GeiserX/PiSpot-Watch/docs/photos/board-stack-battery-wires-side.jpg

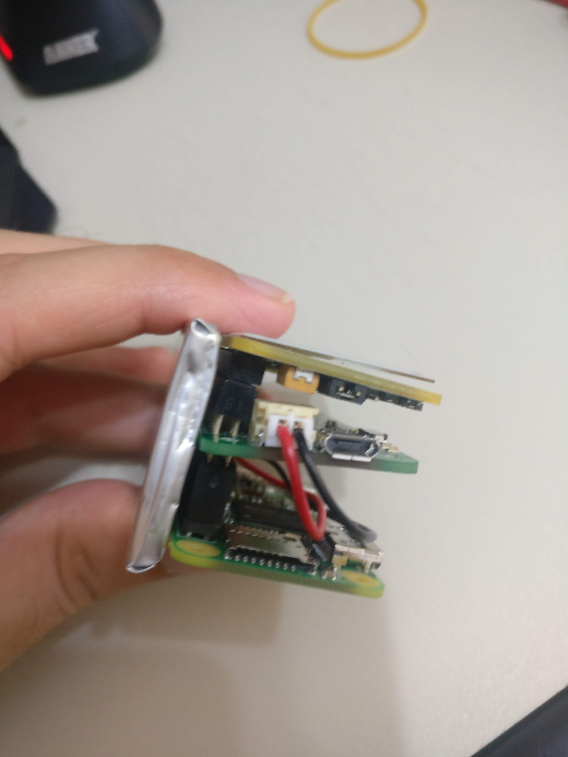
docs/photos/board-stack-battery-wires-side.jpg
