GeiserX/PiSpot-Watch/docs/photos/board-stack-blank-eink-sdcard.jpg

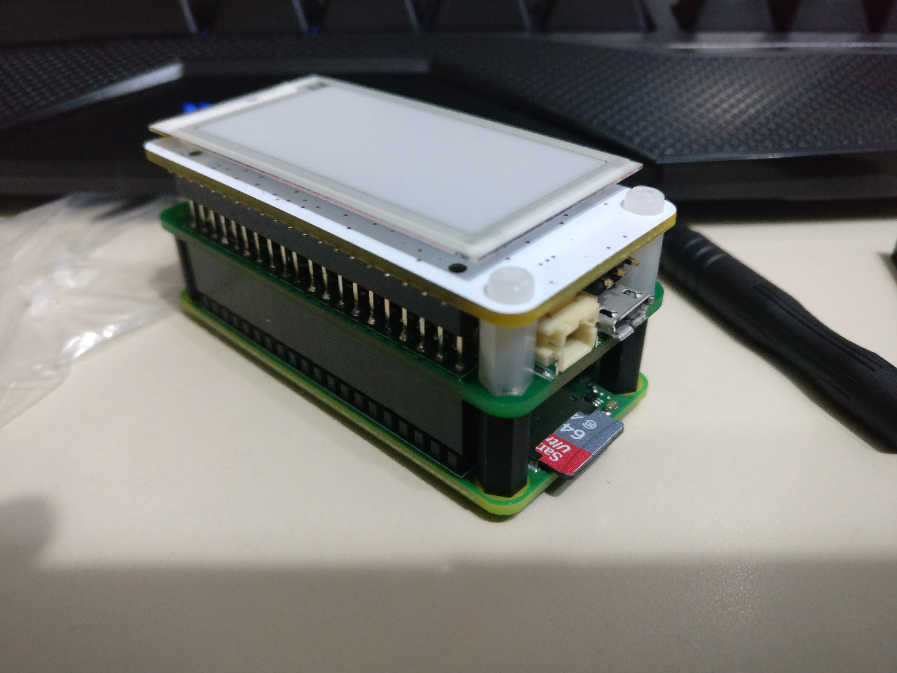
docs/photos/board-stack-blank-eink-sdcard.jpg
