GeiserX/PiSpot-Watch/docs/photos/board-stack-brass-standoffs-front.jpg

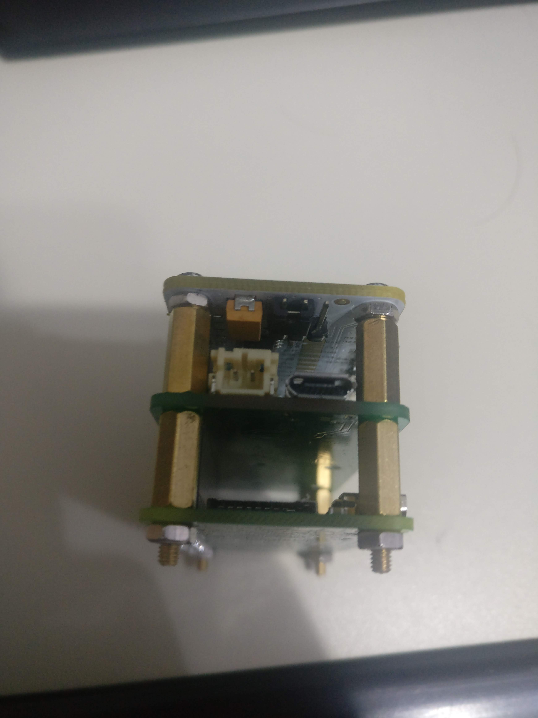
docs/photos/board-stack-brass-standoffs-front.jpg
