GeiserX/PiSpot-Watch/docs/photos/board-stack-brass-standoffs-side.jpg

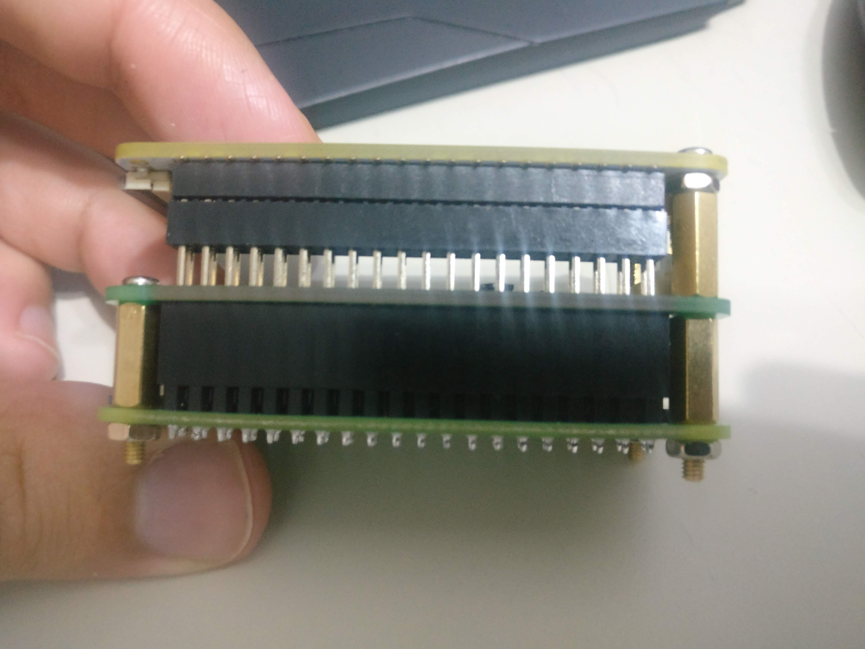
docs/photos/board-stack-brass-standoffs-side.jpg
