GeiserX/PiSpot-Watch/docs/photos/board-stack-in-hand.jpg

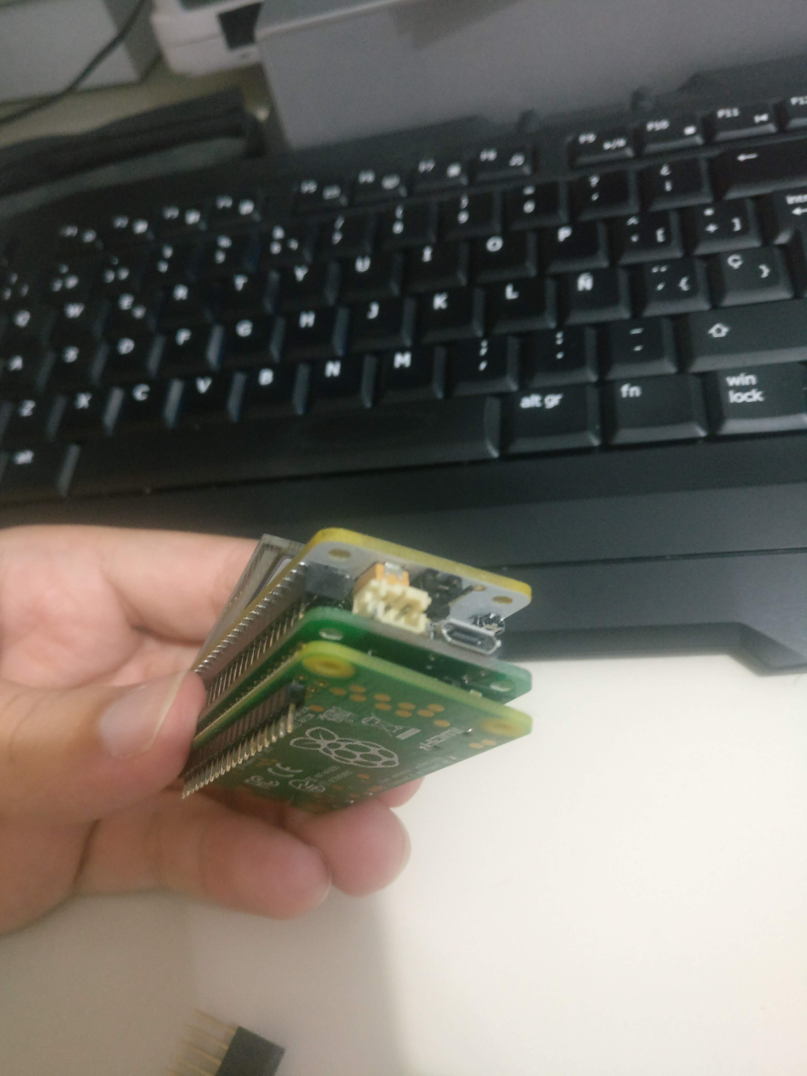
docs/photos/board-stack-in-hand.jpg
