GeiserX/PiSpot-Watch/docs/photos/board-stack-side-profile.jpg

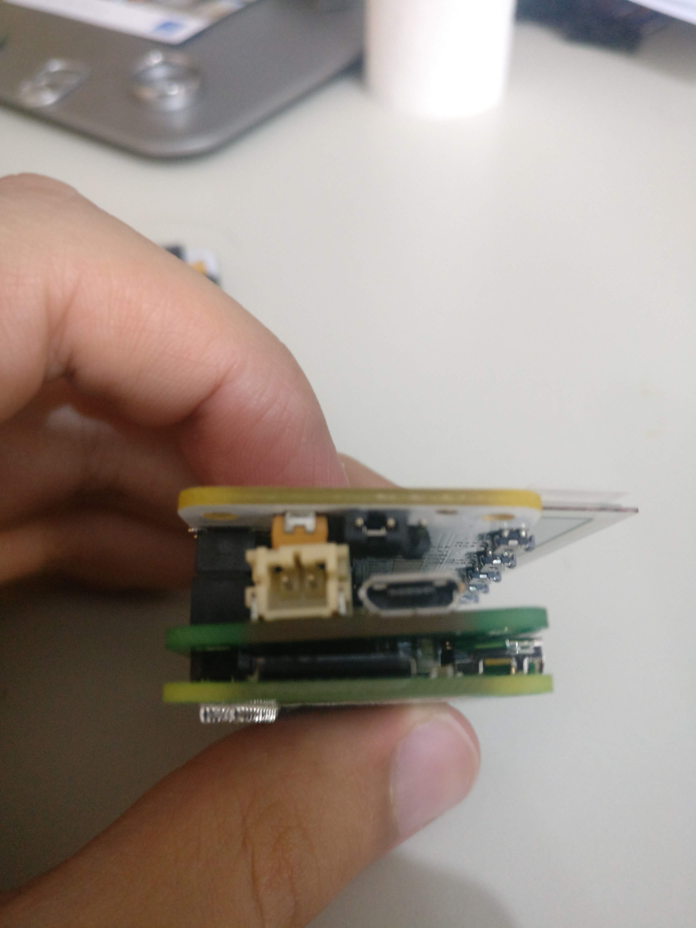
docs/photos/board-stack-side-profile.jpg
