GeiserX/PiSpot-Watch/docs/photos/board-stack-with-battery-side.jpg

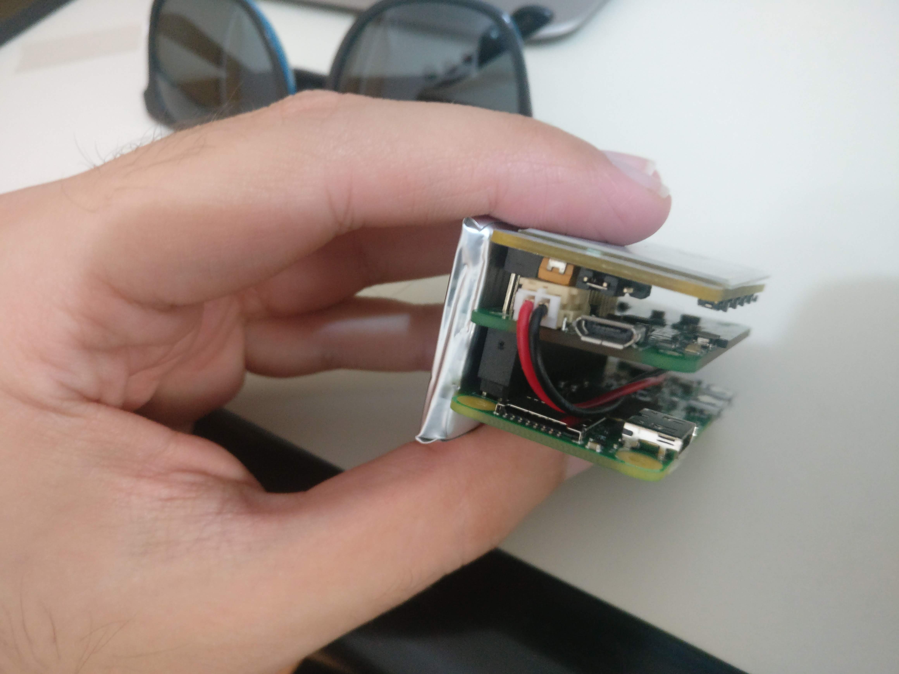
docs/photos/board-stack-with-battery-side.jpg
