GeiserX/PiSpot-Watch/docs/photos/button-panel-side-view.jpg

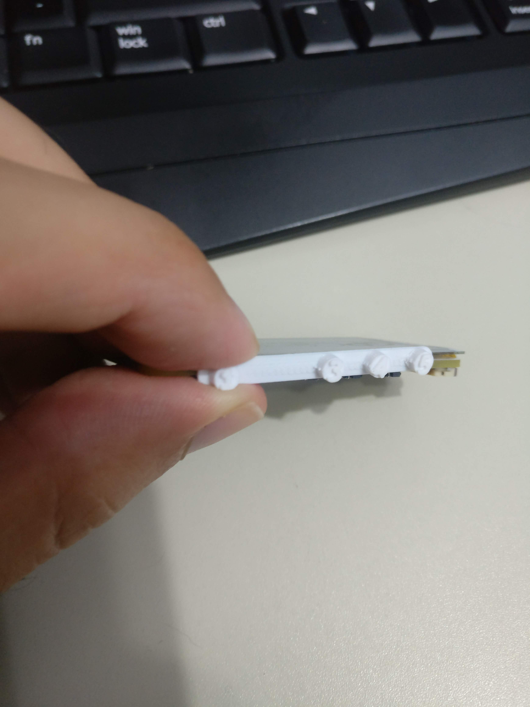
docs/photos/button-panel-side-view.jpg
