GeiserX/PiSpot-Watch/docs/photos/lipo-batteries-1200mah.jpg

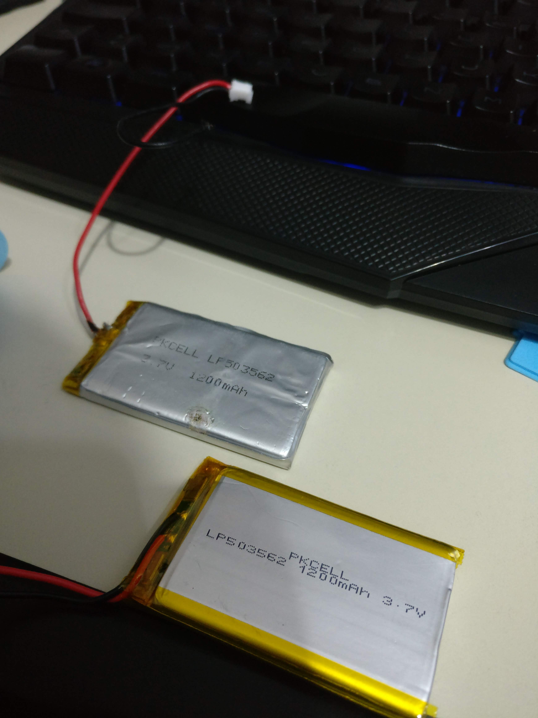
docs/photos/lipo-batteries-1200mah.jpg
