GeiserX/PiSpot-Watch/docs/photos/pi-zero-w-board-back.jpg

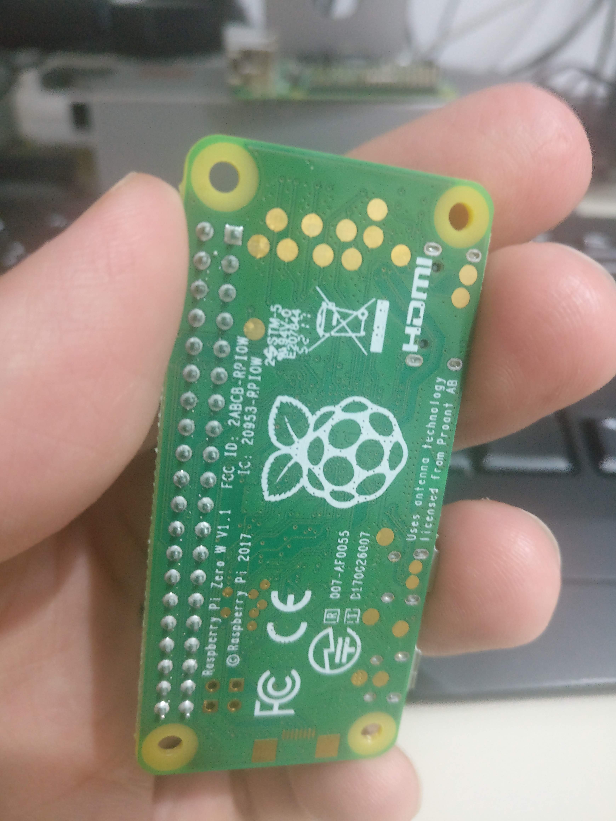
docs/photos/pi-zero-w-board-back.jpg
