GeiserX/PiSpot-Watch/docs/photos/watch-black-case-hdmi-side.jpg

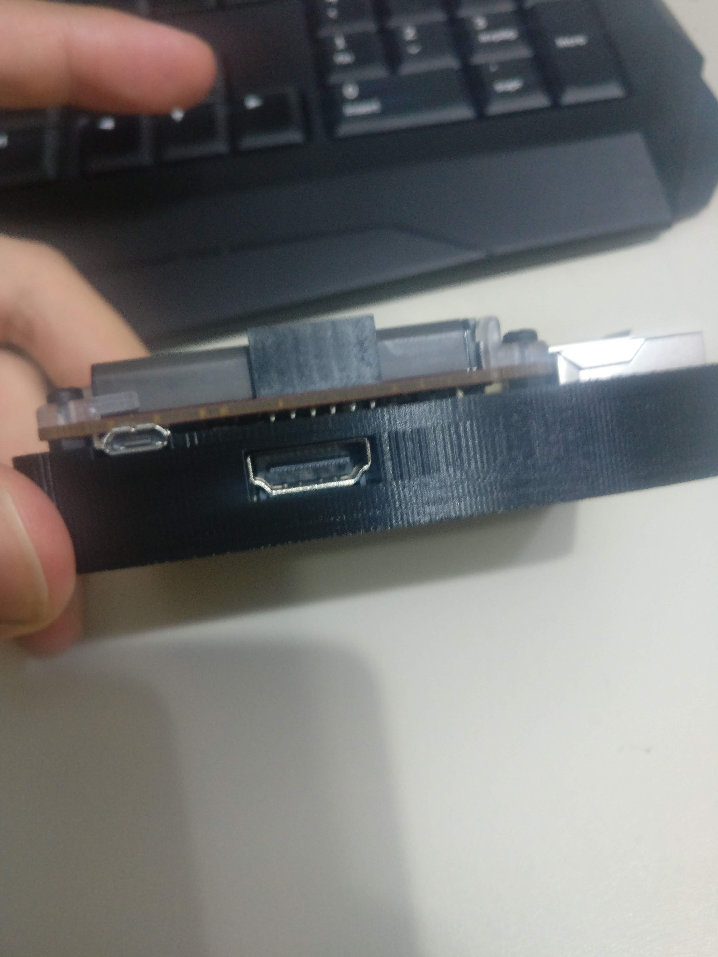
docs/photos/watch-black-case-hdmi-side.jpg
