GeiserX/PiSpot-Watch/docs/photos/3d-printed-case-empty.jpg

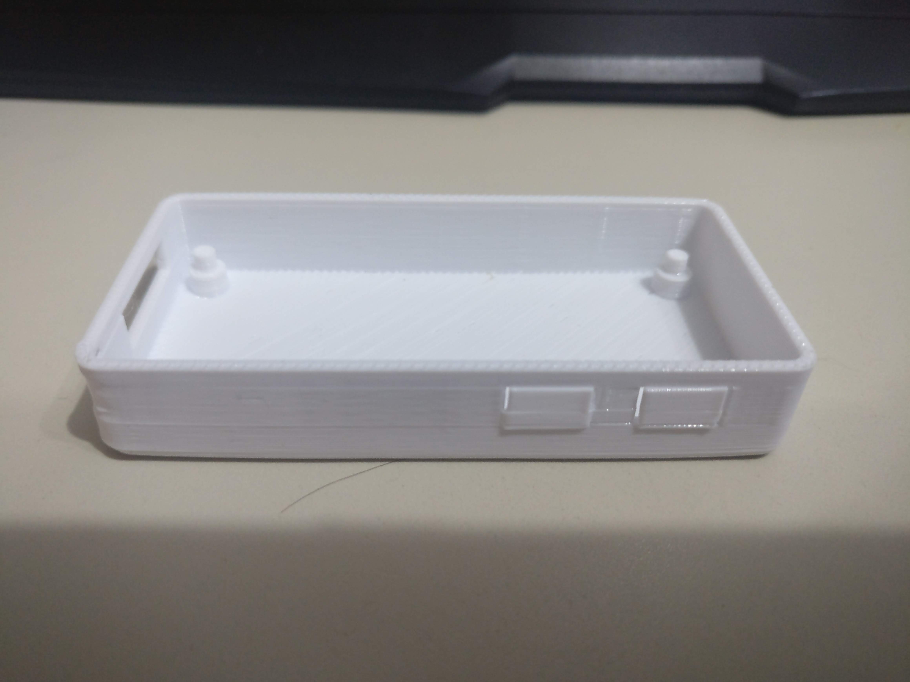
docs/photos/3d-printed-case-empty.jpg
