GeiserX/PiSpot-Watch/docs/photos/caliper-measurement-height.jpg

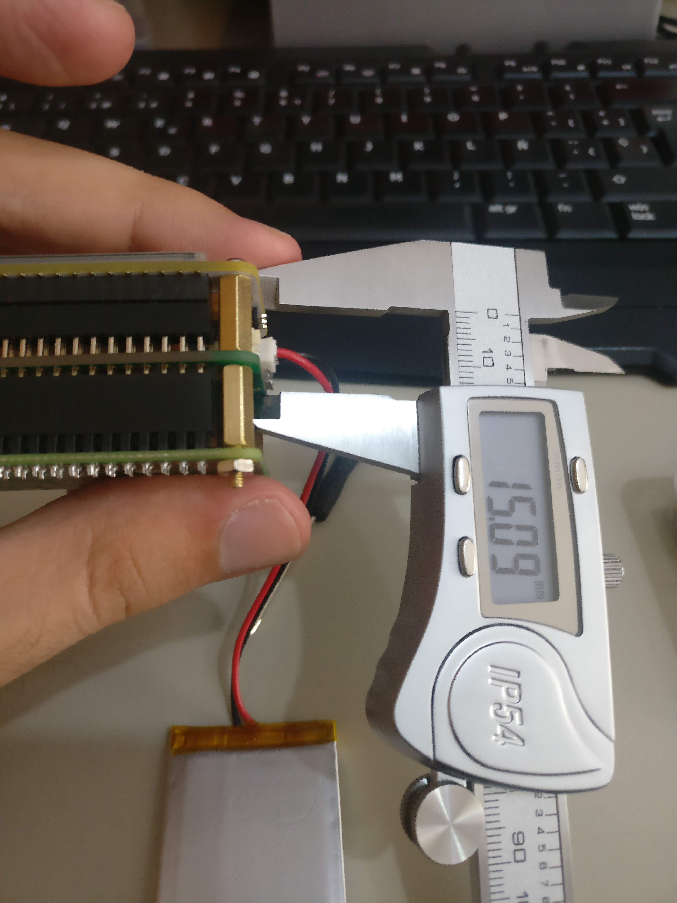
docs/photos/caliper-measurement-height.jpg
