GeiserX/PiSpot-Watch/docs/photos/caliper-measurement-width.jpg

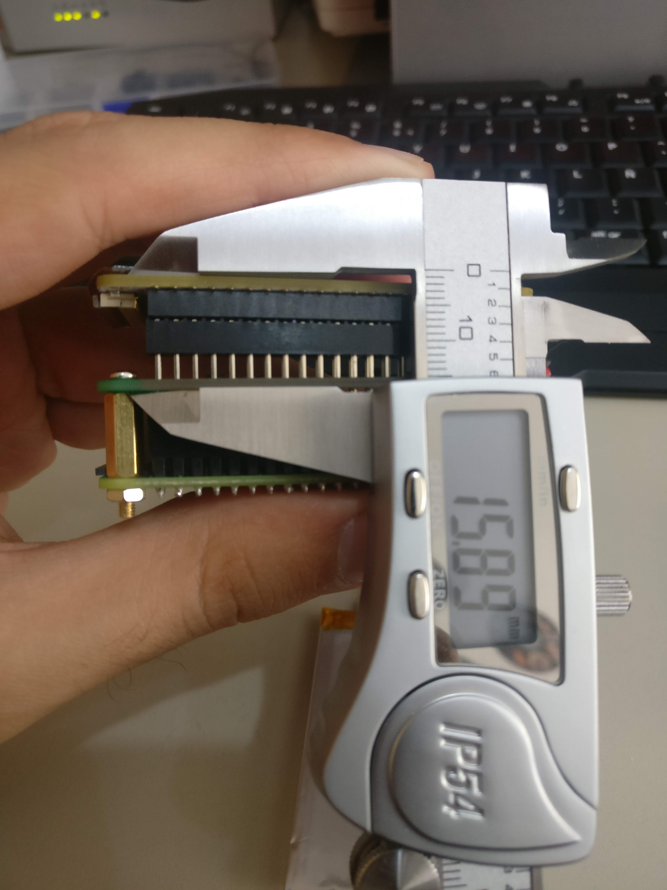
docs/photos/caliper-measurement-width.jpg
